CTSchorsch/tauchlampe/doc/bilder/IMG_6927.JPG

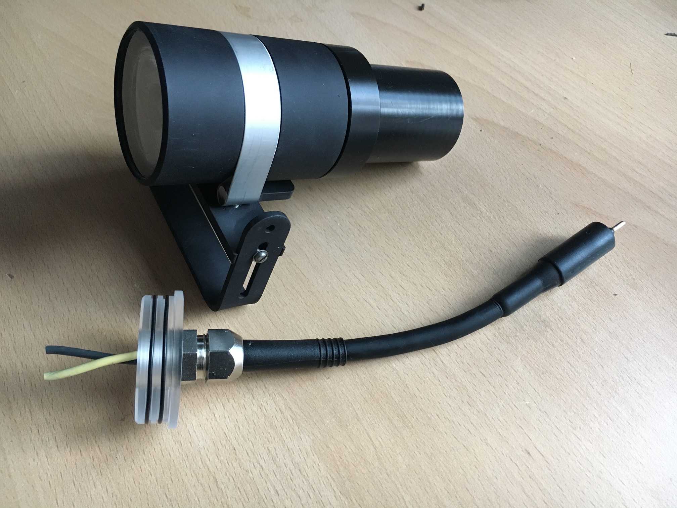
doc/bilder/IMG_6927.JPG
