CTSchorsch/tauchlampe/doc/bilder/IMG_6953.JPG

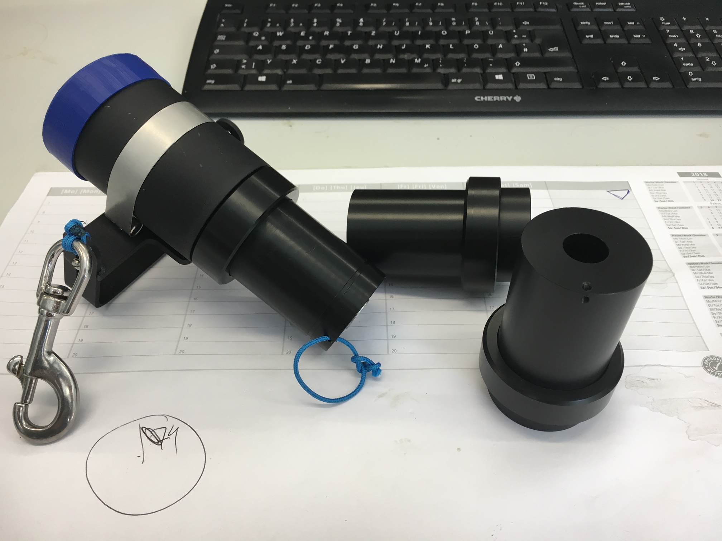
doc/bilder/IMG_6953.JPG
