CTSchorsch/tauchlampe/doc/bilder/IMG_9112.jpg

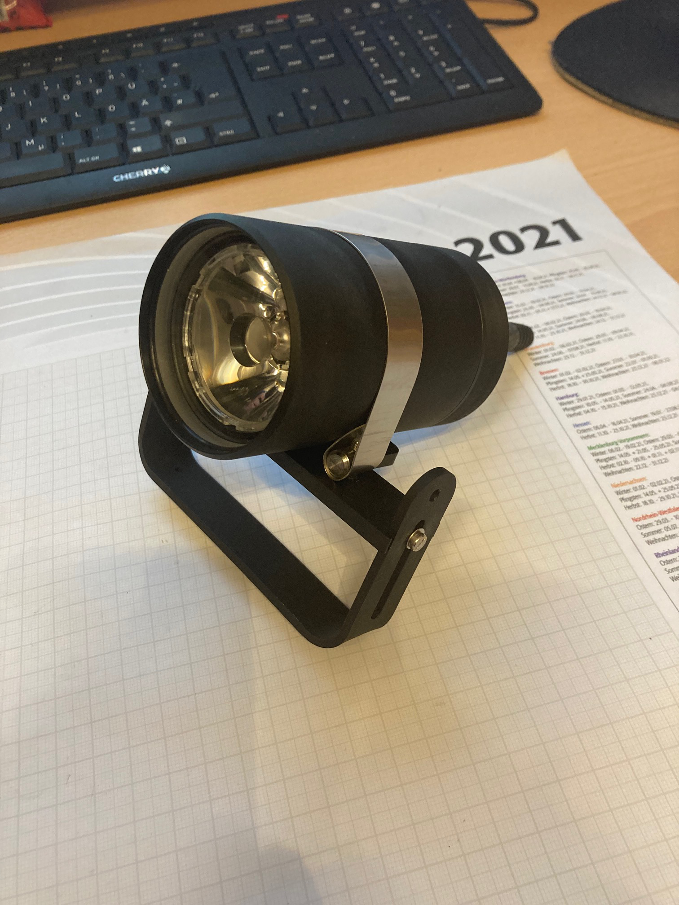
doc/bilder/IMG_9112.jpg
