CTSchorsch/tauchlampe/doc/bilder/pcb_v5.jpg

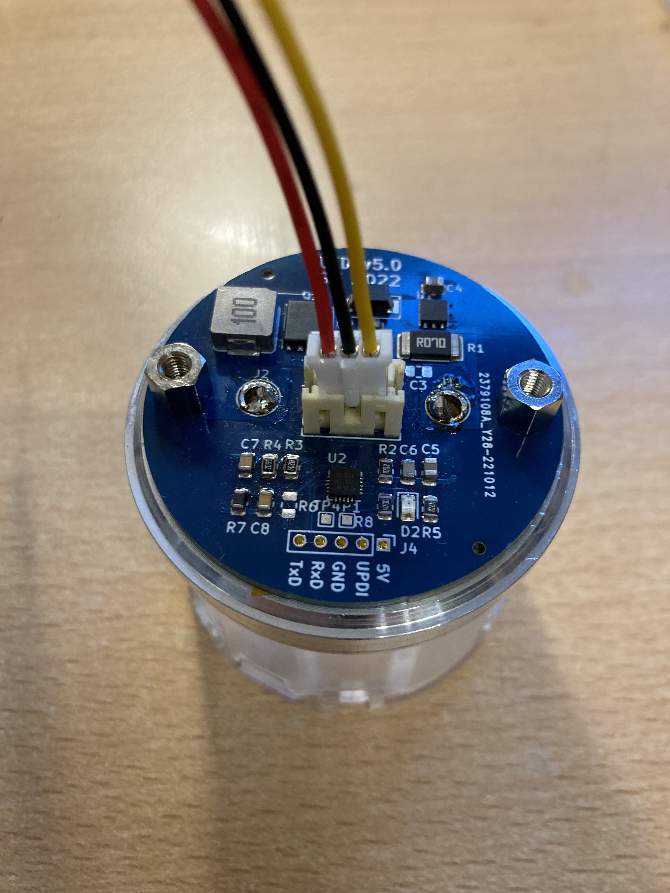
doc/bilder/pcb_v5.jpg
