CTSchorsch/tauchlampe/doc/bilder/v4.2/Batteriefach00.JPG

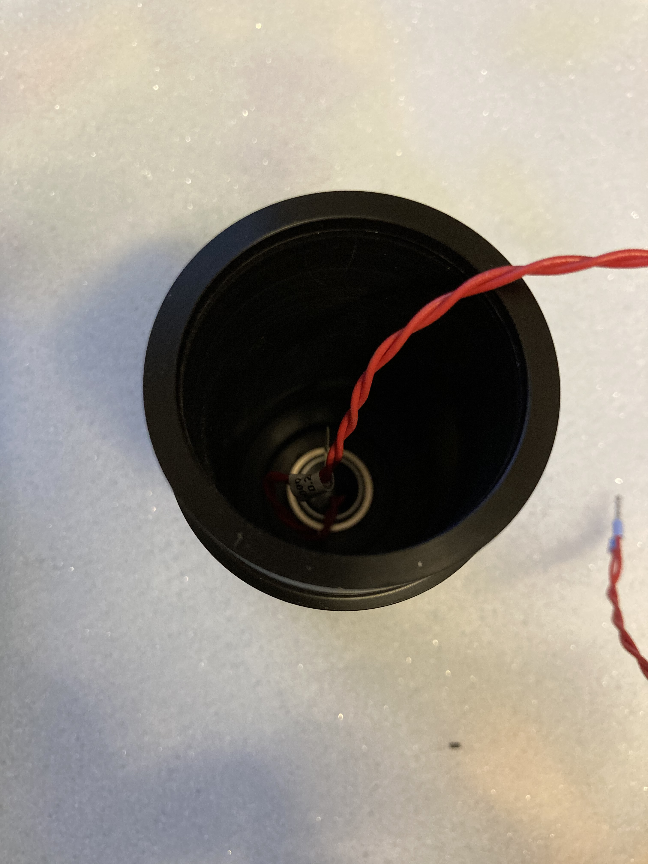
doc/bilder/v4.2/Batteriefach00.JPG
