CTSchorsch/tauchlampe/doc/bilder/v4.2/Batteriefach2.JPG

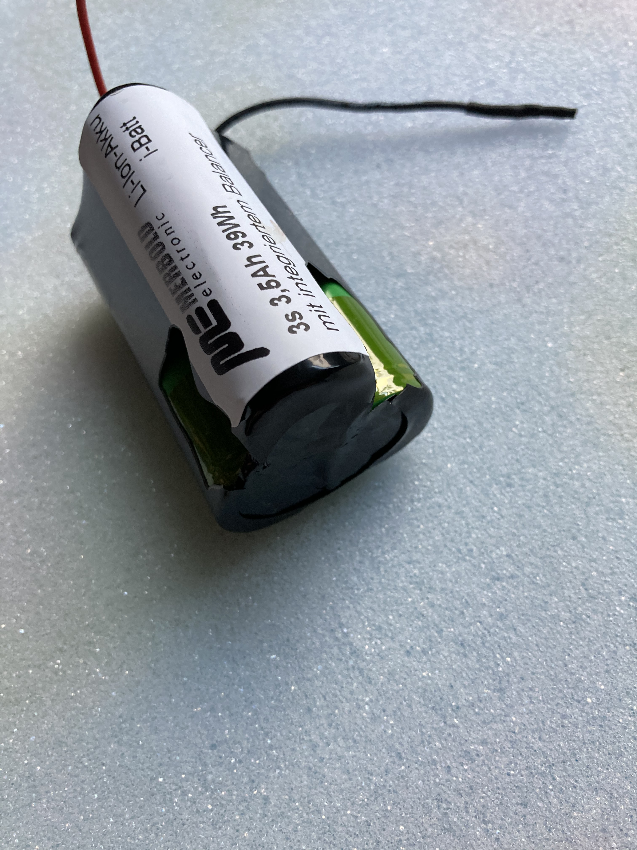
doc/bilder/v4.2/Batteriefach2.JPG
