CTSchorsch/tauchlampe/doc/bilder/v4.2/Batteriefach3.JPG

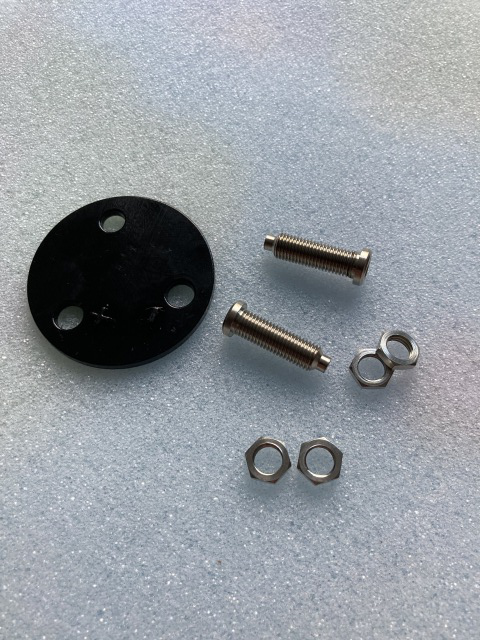
doc/bilder/v4.2/Batteriefach3.JPG
