CTSchorsch/tauchlampe/doc/bilder/v4.2/Batteriefach4.JPG

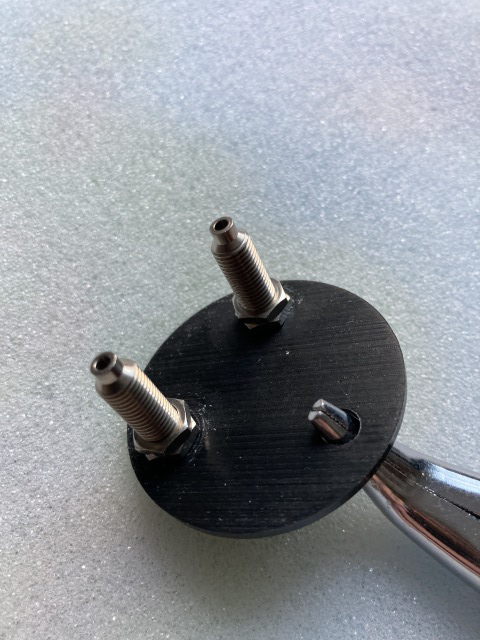
doc/bilder/v4.2/Batteriefach4.JPG
