CTSchorsch/tauchlampe/doc/bilder/v4.2/Batteriefach5.JPG

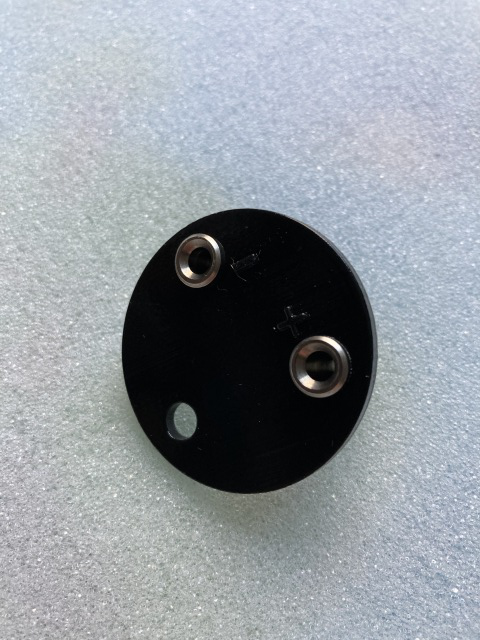
doc/bilder/v4.2/Batteriefach5.JPG
