CTSchorsch/tauchlampe/doc/bilder/v4.2/Batteriefach6.JPG

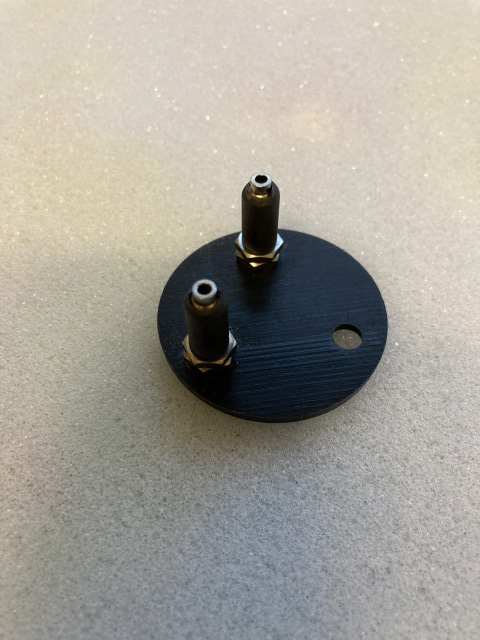
doc/bilder/v4.2/Batteriefach6.JPG
