CTSchorsch/tauchlampe/doc/bilder/v4.2/Batteriefach9.JPG

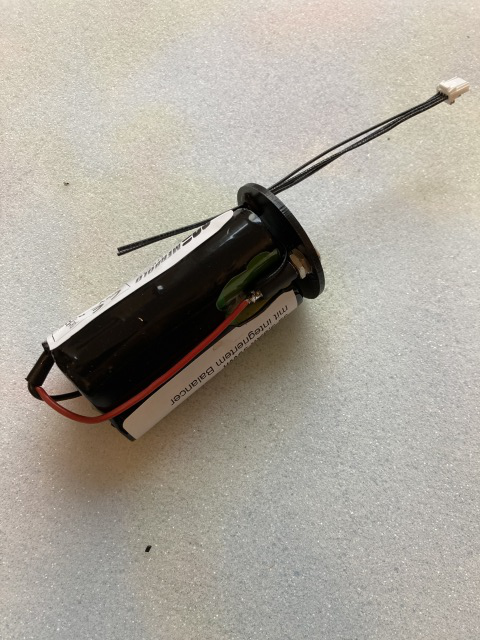
doc/bilder/v4.2/Batteriefach9.JPG
