CTSchorsch/tauchlampe/doc/bilder/v4.2/Batteriefach10.JPG

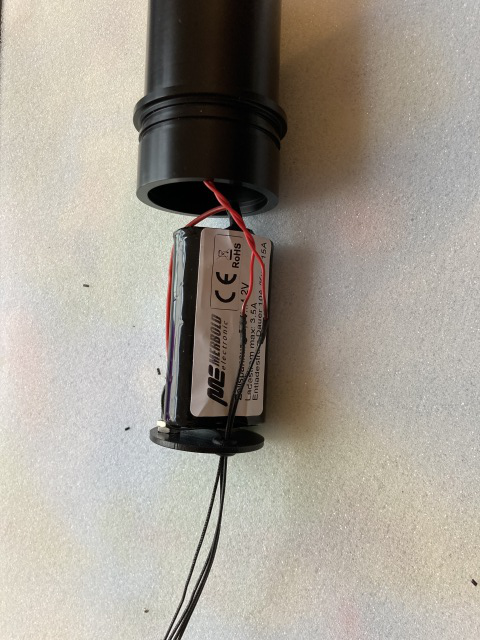
doc/bilder/v4.2/Batteriefach10.JPG
