CTSchorsch/tauchlampe/doc/bilder/v4.2/Batteriefach11.JPG

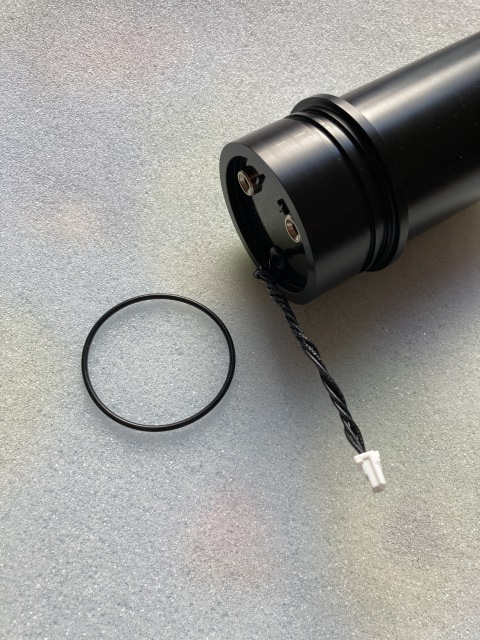
doc/bilder/v4.2/Batteriefach11.JPG
