CTSchorsch/tauchlampe/doc/bilder/v4.2/halterung2.jpg

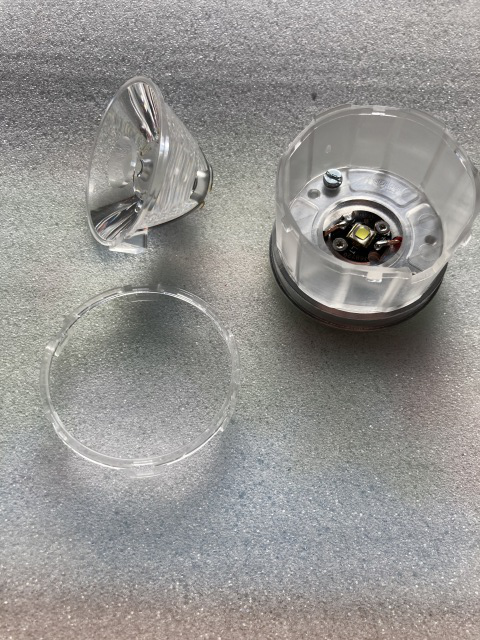
doc/bilder/v4.2/halterung2.jpg
