CTSchorsch/tauchlampe/doc/bilder/v4.2/halterung3.jpg

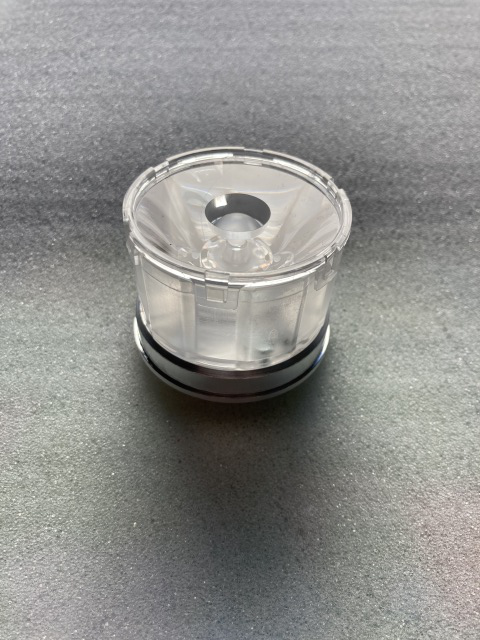
doc/bilder/v4.2/halterung3.jpg
