CTSchorsch/tauchlampe/doc/bilder/v4.2/halterung.jpg

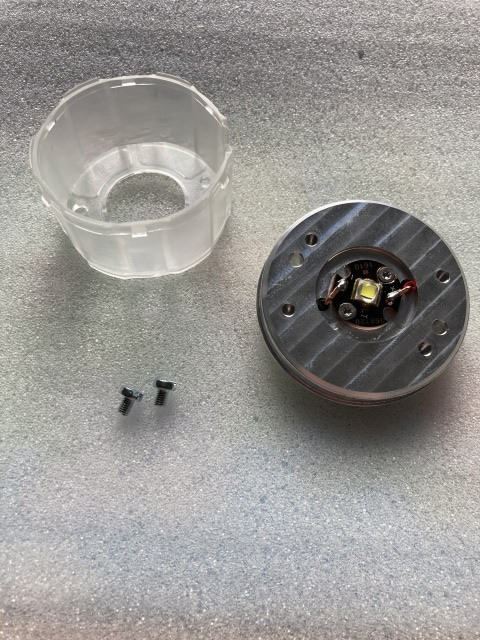
doc/bilder/v4.2/halterung.jpg
