CTSchorsch/tauchlampe/mech/Tools/Thumbloop/LoopA.bmp

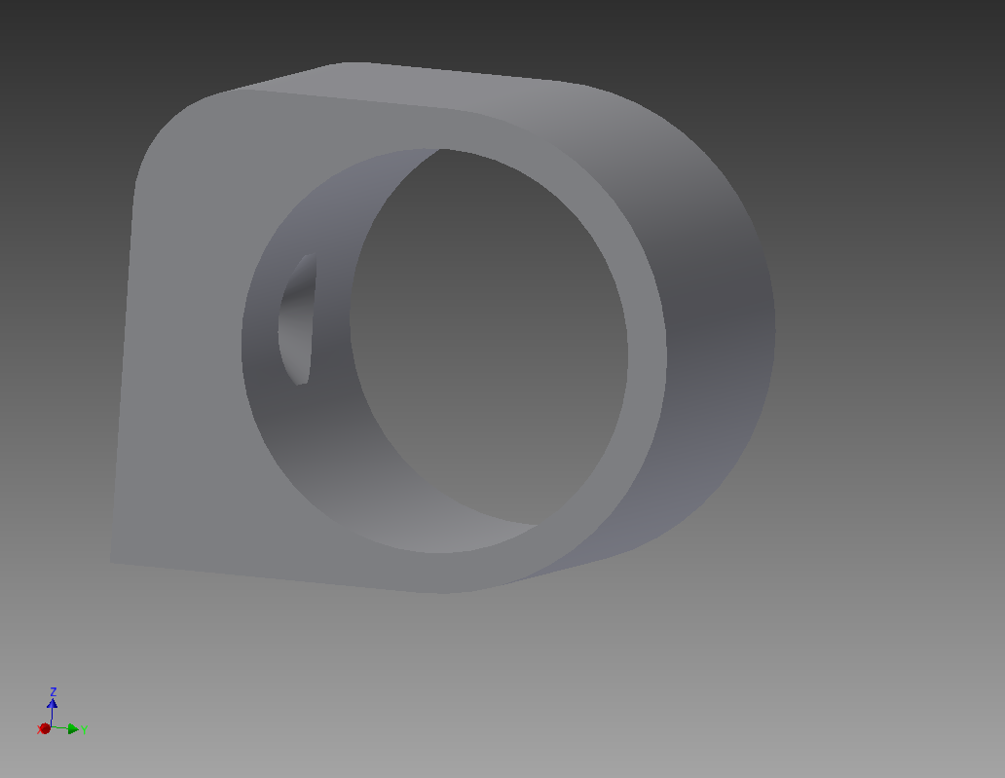
mech/Tools/Thumbloop/LoopA.bmp
