CTSchorsch/tauchlampe/mech/Tools/Thumbloop/LoopB.bmp

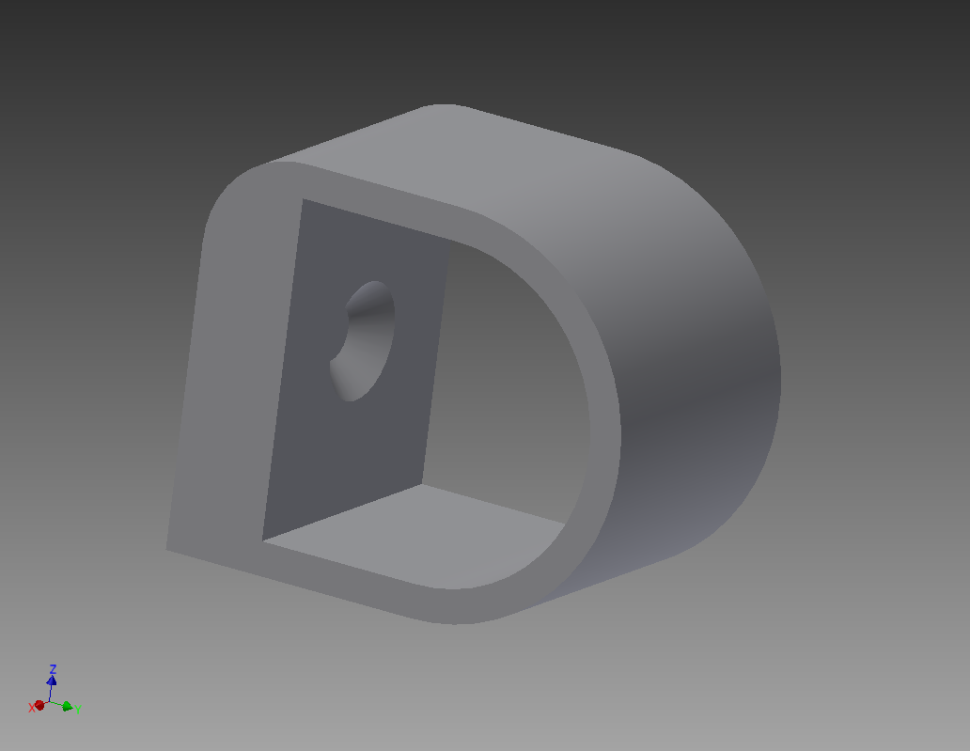
mech/Tools/Thumbloop/LoopB.bmp
