CTSchorsch/tauchlampe/mech/Tools/Thumbloop/LoopC.bmp

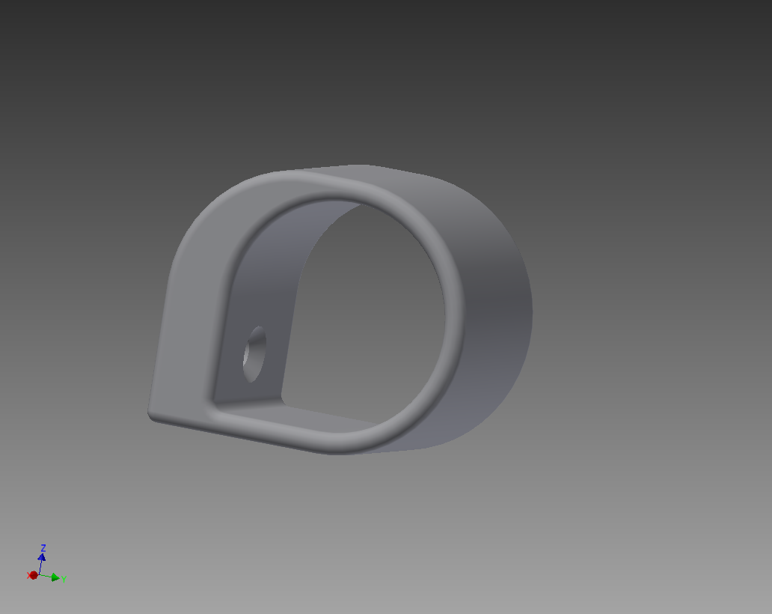
mech/Tools/Thumbloop/LoopC.bmp
